nemesa/treadmill-controller/project-pictures/finished_1.jpg

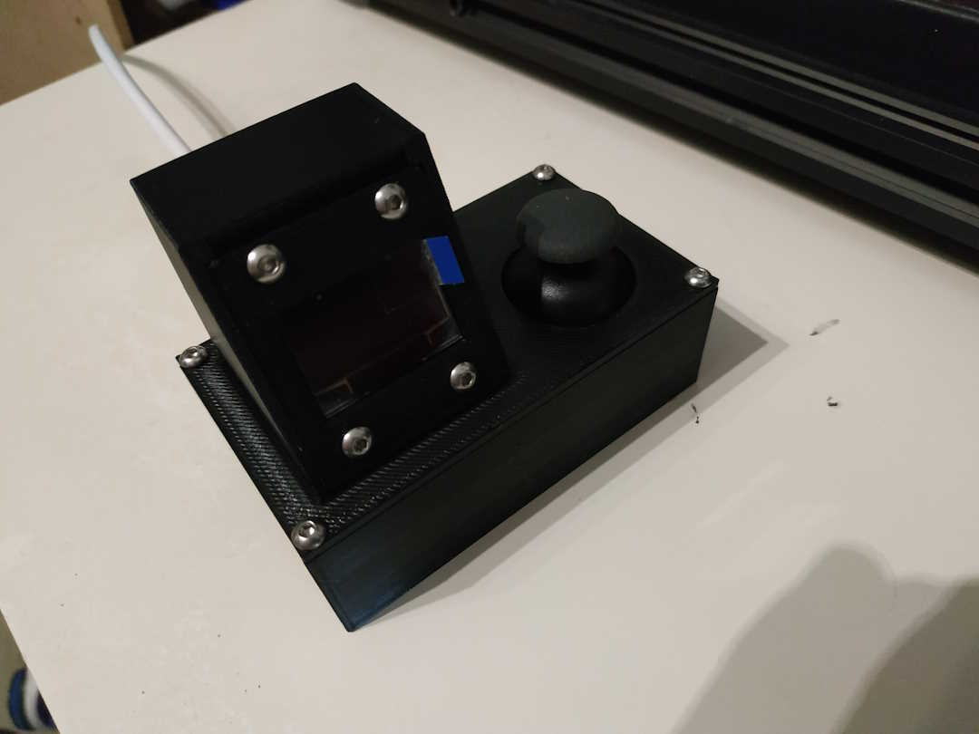
project-pictures/finished_1.jpg
