nemesa/treadmill-controller/project-pictures/finished_2.jpg

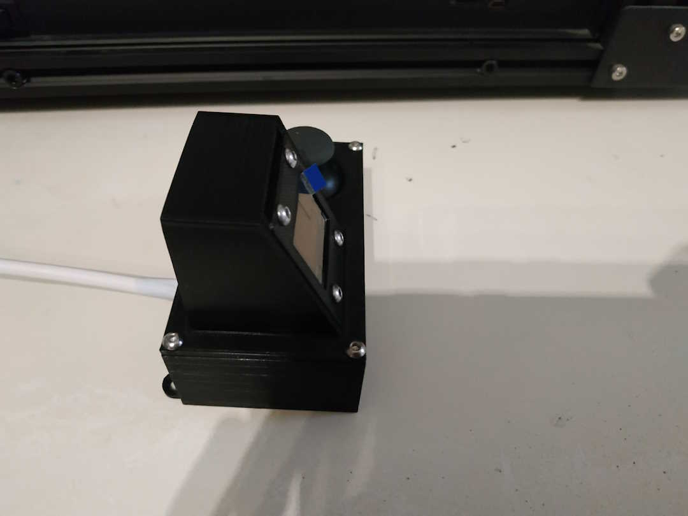
project-pictures/finished_2.jpg
