nemesa/treadmill-controller/project-pictures/prototype_01.jpg

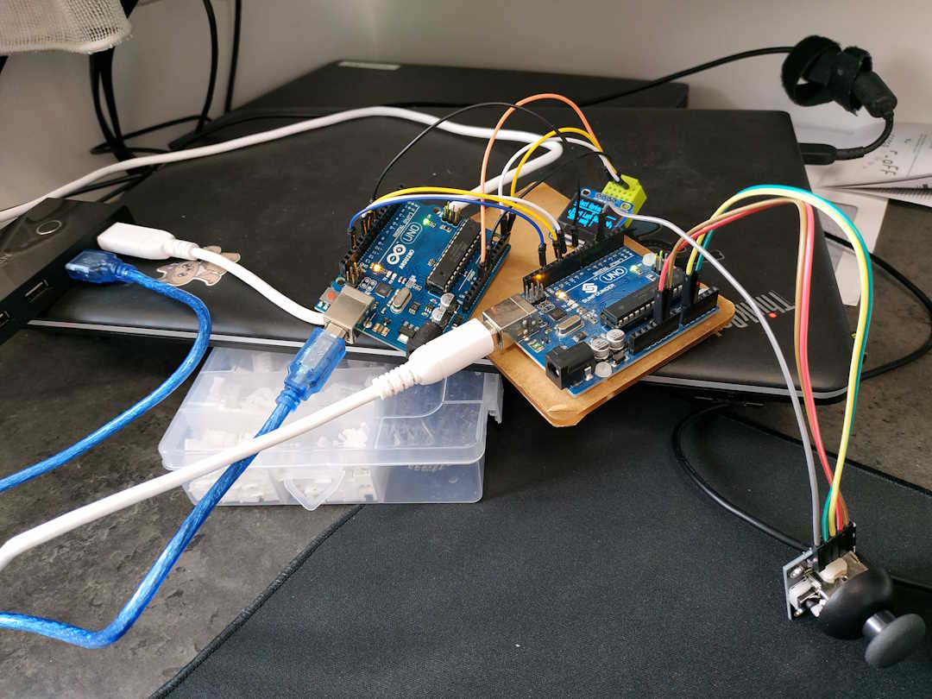
project-pictures/prototype_01.jpg
