nemesa/treadmill-controller/project-pictures/prototype_02.jpg

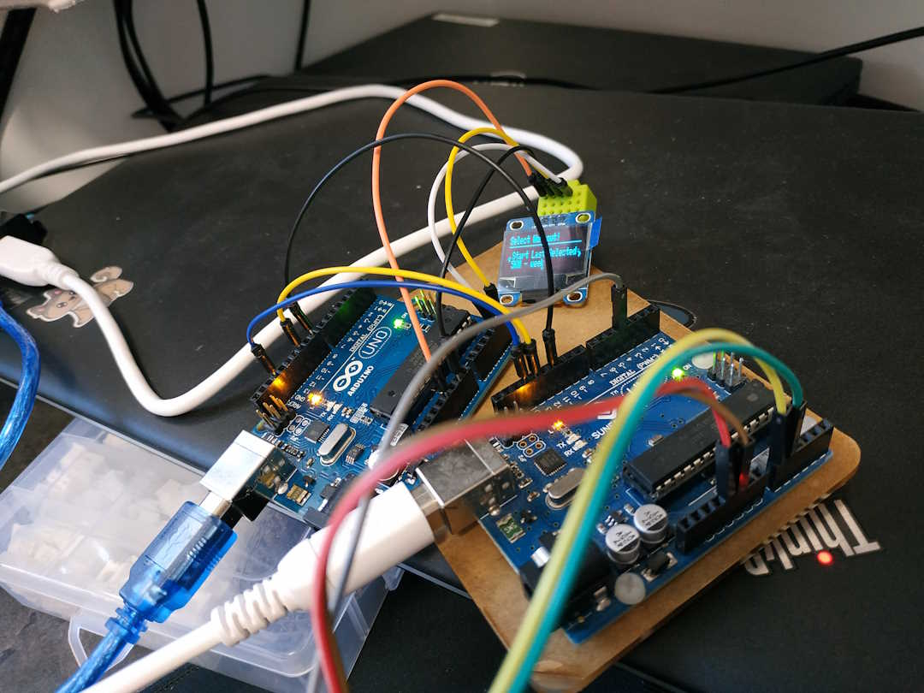
project-pictures/prototype_02.jpg
