nemesa/treadmill-controller/project-pictures/assembly_01.jpg

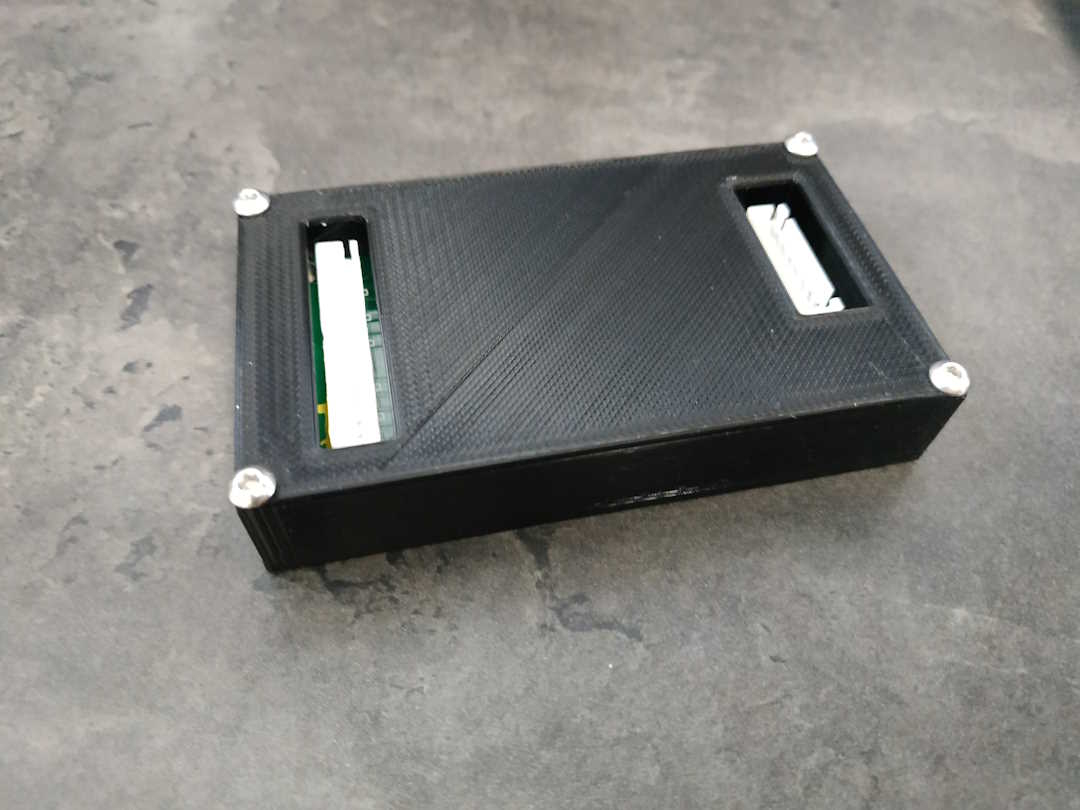
project-pictures/assembly_01.jpg
