nemesa/treadmill-controller/project-pictures/assembly_07.jpg

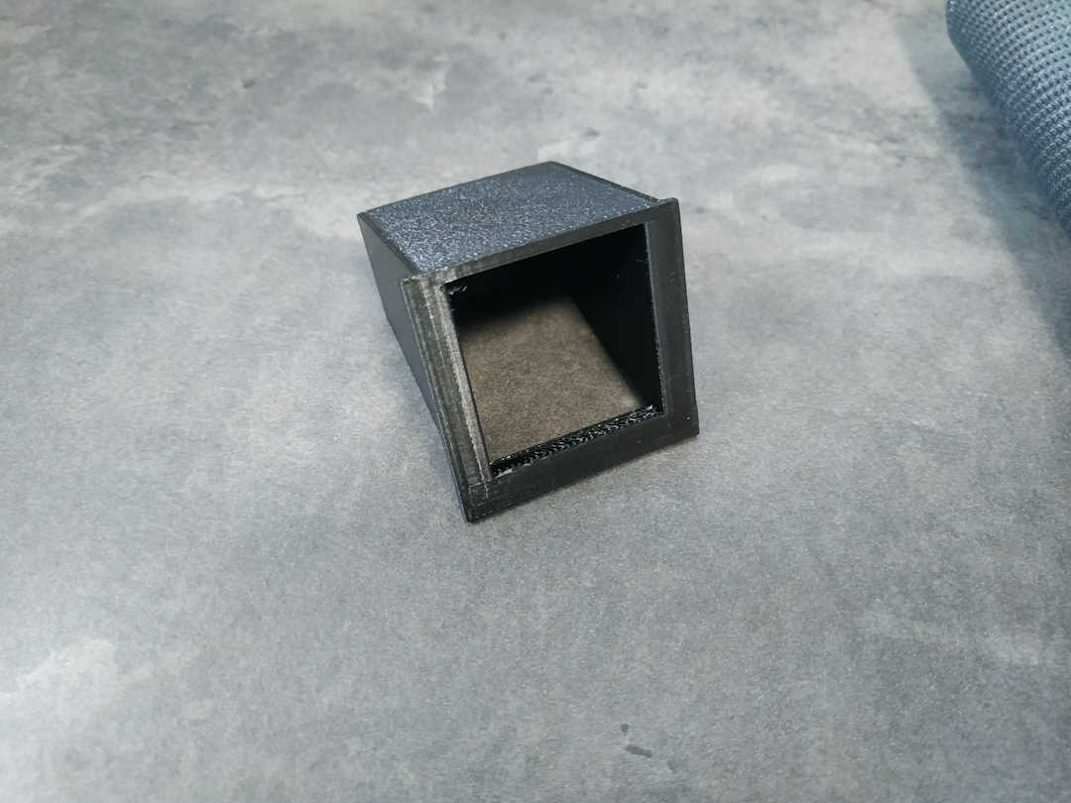
project-pictures/assembly_07.jpg
