nemesa/treadmill-controller/project-pictures/assembly_10.jpg

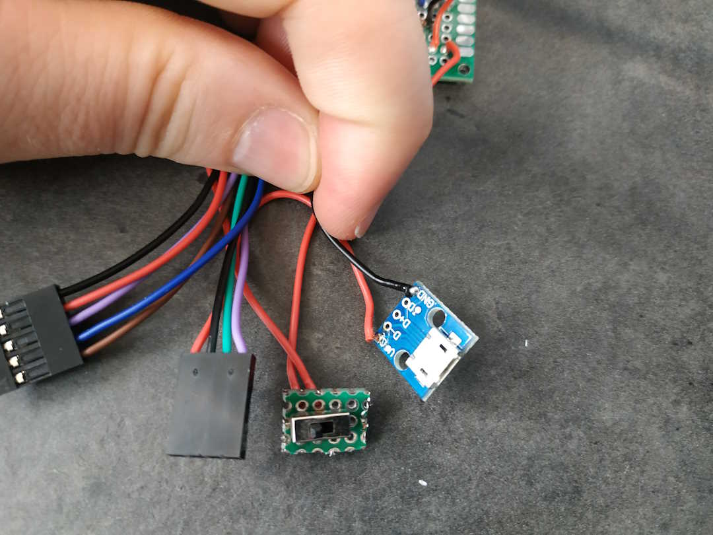
project-pictures/assembly_10.jpg
