nemesa/treadmill-controller/controller/controlpinmap.h

#ifndef ControlPinMapStruct_h
#define ControlPinMapStruct_h

struct ControlPinMapStruct {
  uint8_t startStop;
  uint8_t speedInc;
  uint8_t speedDec;
  uint8_t speed30;
  uint8_t speed60;
  uint8_t speed100;
  uint8_t holdDelay;
  uint8_t pressDelay;
  
};

#endif
