nemesa/treadmill-controller/controller/relay.cpp

#include "Arduino.h"
#include "relay.h"
#include "relay.h"
#include "controlpinmap.h"

RelayHandler::RelayHandler(int pin1, int pin2, int pin3, int pin4, int pin5, int pin6) {
  _pin1 = pin1;
  _pin2 = pin2;
  _pin3 = pin3;
  _pin4 = pin4;
  _pin5 = pin5;
  _pin6 = pin6;
}

void RelayHandler::setup() {
  Serial.println(F("RelayHandler-setup"));

  pinMode(_pin1, OUTPUT);
  pinMode(_pin2, OUTPUT);
  pinMode(_pin3, OUTPUT);
  pinMode(_pin4, OUTPUT);
  pinMode(_pin5, OUTPUT);
  pinMode(_pin6, OUTPUT);
}

void RelayHandler::start(ControlPinMapStruct* pinMap) {
  Serial.println(F("RelayHandler-start "));
  if (!isRunning) {
    isRunning = true;
    currentSpeed = 10;
    sendSignal(pinMap, pinMap->startStop);
  }
}

void RelayHandler::stop(ControlPinMapStruct* pinMap) {
  Serial.println(F("RelayHandler-stop "));
  if (isRunning) {
    isRunning = false;
    currentSpeed = 0;
    sendSignal(pinMap, pinMap->startStop);
  }
}
void RelayHandler::toSpeed(ControlPinMapStruct* pinMap, uint8_t speed) {
  Serial.print(F("RelayHandler-speed "));
  Serial.println(speed);

  if (currentSpeed == speed) {
    return;
  }


  if (speed < 45) {
    currentSpeed = 30;
    sendSignal(pinMap, pinMap->speed30);

  } else if (speed < 75) {
    currentSpeed = 60;
    sendSignal(pinMap, pinMap->speed60);
  } else {
    currentSpeed = 100;
    sendSignal(pinMap, pinMap->speed100);
  }

  if (currentSpeed != speed) {
    int numberToTarget = 0;
    if (currentSpeed > speed) {
      numberToTarget = currentSpeed - speed;
    } else {
      numberToTarget = speed - currentSpeed;
    }

    Serial.print(F("numberToTarget "));
    Serial.print(numberToTarget);
    Serial.print(F(" currentSpeed "));
    Serial.print(currentSpeed);
    Serial.print(F(" speed "));
    Serial.println(speed);

    for (int i = 0; i < numberToTarget; i++) {
      if (currentSpeed > speed) {
        currentSpeed--;
        sendSignal(pinMap, pinMap->speedDec);
      } else {
        currentSpeed++;
        sendSignal(pinMap, pinMap->speedInc);
      }
    }
  }
}

void RelayHandler::pinTest(ControlPinMapStruct* pinMap, uint8_t pinNo) {
  Serial.print(F("RelayHandler-pinTest "));
  Serial.println(pinNo);
  if (pinNo > 0 && pinNo < 7) {
    sendSignal(pinMap, pinNo);
  } else {
    sendSignal(pinMap, 1);
  }
}

void RelayHandler::sendSignal(ControlPinMapStruct* pinMap, uint8_t pinNo) {
  Serial.print(F("RelayHandler-sendSignal on pin:"));
  Serial.print(pinNo);
  Serial.print(F(" currentSpeed:"));
  Serial.println(currentSpeed);

  uint8_t pin = _pin1;
  if (pinNo == 2) {
    pin = _pin2;
  }
  if (pinNo == 3) {
    pin = _pin3;
  }
  if (pinNo == 4) {
    pin = _pin4;
  }
  if (pinNo == 5) {
    pin = _pin5;
  }
  if (pinNo == 6) {
    pin = _pin6;
  }


  digitalWrite(pin, HIGH);
  delay(pinMap->holdDelay * 10);
  digitalWrite(pin, LOW);
  delay(pinMap->pressDelay * 10);
}
