nemesa/treadmill-controller/controller/eeprom.h

#ifndef EEPROMHandler_h
#define EEPROMHandler_h

#include "userdata.h"
#include "controlpinmap.h"

class EEPROMHandler {
public:
  EEPROMHandler();
  void setup();
  void wipeAll();
  void setLastUser(uint8_t num);
  UserDataStruct getLastSelectedUser();
  void writeUserData(struct UserDataStruct user);
  UserDataStruct readUser(uint8_t num);
  ControlPinMapStruct getControlPinMap();
  void writeControlPinMap(struct ControlPinMapStruct map);
private:
};

#endif
